mengstr/PlingPlong/Firmware/Controller/PlingPlong.X/easteregg.c

#include <stdint.h>         // uint8_t definitions
#include <string.h>         // strcpy for easteregg
#include <usart.h>

#include "config.h"
#include "dispbut.h"
#include "touch.h"
#include "easteregg.h"



const uint16_t hadLeds[]={
    0x7c9f,0x43f0,0x43f0,0x729f,    //  HTTP
    0x0140,0x6083,0x6083,0x7c9f,    //  ://H
    0x3e8f,0x462e,0x6c9f,0x3e8f,    //  ACKA
    0x3a3f,0x3e8f,0x60f8,0x0020,    //  DAY.
    0x462e,0x7e3f,0x7d9f            //  COM
};


//
// MIDI converted by Miditones https://code.google.com/p/miditones/ made by Len Shustek
//
const uint8_t eeMidiNyan [] = {
0x90,87, 0,102, 0x80, 0,3, 0x90,88, 0,102, 0x80, 0,3, 0x90,90, 0,102, 0x80, 0,109,
0x90,95, 0,102, 0x80, 0,3, 0x90,88, 0,102, 0x80, 0,3, 0x90,87, 0,102, 0x80, 0,3,
0x90,88, 0,102, 0x80, 0,3, 0x90,90, 0,102, 0x80, 0,3, 0x90,95, 0,102, 0x80, 0,3,
0x90,99, 0,102, 0x80, 0,3, 0x90,100, 0,102, 0x80, 0,3, 0x90,99, 0,102, 0x80, 0,3,
0x90,94, 0,102, 0x80, 0,3, 0x90,95, 0,102, 0x80, 0,109, 0x90,90, 0,102, 0x80, 0,109,
0x90,87, 0,102, 0x80, 0,3, 0x90,88, 0,102, 0x80, 0,3, 0x90,90, 0,102, 0x80, 0,109,
0x90,95, 0,102, 0x80, 0,109, 0x90,97, 0,102, 0x80, 0,3, 0x90,94, 0,102, 0x80, 0,3,
0x90,95, 0,102, 0x80, 0,3, 0x90,97, 0,102, 0x80, 0,3, 0x90,100, 0,102, 0x80, 0,3,
0x90,99, 0,102, 0x80, 0,3, 0x90,100, 0,102, 0x80, 0,3, 0x90,97, 0,102, 0x80, 0,3,
0x90,40, 0x91,78, 0,207, 0x81, 0,3, 0x80, 0x90,80, 0x91,52, 0,207, 0x80, 0,3, 0x81, 0x90,74,
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
0,117, 0x82, 0x80, 0,4, 0x90,37, 0x91,44, 0x92,49, 0,229, 0x80, 0x81, 0x82, 0,4, 0x90,35,
0x91,42, 0x92,47, 0,117, 0x93,68, 0,112, 0x83, 0,4, 0x93,68, 0,229, 0x80, 0x81, 0x82, 0x83,
0,4, 0x90,35, 0x91,68, 0x92,42, 0x93,80, 0,229, 0x81, 0x83, 0x80, 0x82, 0,4, 0x90,68, 0x91,35,
0x92,80, 0x93,42, 0,229, 0x80, 0x82, 0,4, 0x90,68, 0x92,80, 0,229, 0x81, 0x83, 0x80, 0x82, 0,4,
0x90,35, 0x91,68, 0x92,42, 0x93,80, 0,112, 0x81, 0x83, 0,4, 0x91,68, 0x93,80, 0,112, 0x80,
0x82, 0,4, 0x90,47, 0x92,54, 0,112, 0x83, 0x81, 0,117, 0x82, 0x80, 0,4, 0x90,35, 0x91,42,
0x92,47, 0,229, 0x80, 0x81, 0x82, 0,4, 0x90,68, 0x91,30, 0x92,80, 0x93,37, 0,229, 0x80, 0x82,
0,4, 0x90,68, 0x92,80, 0,229, 0x81, 0x83, 0x80, 0x82, 0,4, 0x90,30, 0x91,68, 0x92,37, 0x93,80,
0,229, 0x81, 0x83, 0x80, 0x82, 0,4, 0x90,68, 0x91,30, 0x92,80, 0x93,37, 0,229, 0x80, 0x82, 0,4,
0x90,68, 0x92,80, 0,229, 0x81, 0x83, 0x80, 0x82, 0,4, 0x90,30, 0x91,68, 0x92,37, 0x93,80, 0,112,
0x81, 0x83, 0,4, 0x91,68, 0x93,80, 0,112, 0x80, 0x82, 0,4, 0x90,42, 0x92,49, 0,112, 0x83,
0x81, 0,117, 0x82, 0x80, 0,4, 0x90,30, 0x91,37, 0x92,42, 0,229, 0x80, 0x81, 0x82, 0,4, 0x90,30,
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
};





void EeNoteOn(uint8_t no) {
    while (Busy2USART());
    Write2USART(0x90|CHANNEL);
    while (Busy2USART());
    Write2USART(no);
    while (Busy2USART());
    Write2USART(VELOCITY);
    __delay_ms(1);
}

void EeNoteOff(uint8_t no) {
    while (Busy2USART());
    Write2USART(0x80|CHANNEL);
    while (Busy2USART());
    Write2USART(no);
    while (Busy2USART());
    Write2USART(VELOCITY);
    __delay_ms(1);
}

void EeSendCC(uint8_t no, uint8_t v) {
    while (Busy2USART());
    Write2USART(0xB0|CHANNEL);
    while (Busy2USART());
    Write2USART(no);
    while (Busy2USART());
    Write2USART(v);
    __delay_ms(1);
}




void EeAllNotesOff(void) {
    uint8_t i;
    for (i=0; i<127; i++) {
        EeNoteOff(i);
    }
}


void EasterEgg(uint8_t mode) {
    uint8_t     i,j;
    uint8_t     tmps[20];
    uint16_t    noteCnt;
    uint8_t     eeChannelTone[16];
    uint8_t     b1,b2;
    uint16_t    ii, dly;
    uint8_t     *pMidi;


    // Step 1 - Silence all channels
    EeAllNotesOff();
    leds=0x00;
    disp[0]=0x00;
    disp[1]=0x00;
    disp[2]=0x00;

    // If mode is 1 display HTTP://HACKADAY.COM on 7-segs
    if (mode==1) {
        //           000111222333444555666777
        strcpy(tmps,"HTTP: // HACKADAY .  COM");
        for (i=0; i<8; i++) {
            disp[0]=charmap[tmps[0+((i)*3)]-32];
            disp[1]=charmap[tmps[1+((i)*3)]-32];
            disp[2]=charmap[tmps[2+((i)*3)]-32];
            for (j=0; j<40; j++) __delay_ms(10);
        }
    }

    // If mode is 2 display HTTP://HACKADAY.COM on the leds
    if (mode==2) {
        for (j=0; j<100; j++) __delay_ms(10);
        for (i=0; i<sizeof(hadLeds)/2; i++) {
            leds=hadLeds[i];
            for (j=0; j<40; j++) __delay_ms(10);
            leds=0;
            for (j=0; j<5; j++) __delay_ms(10);
        }
    }

    disp[0]=0x00;
    disp[1]=0x00;
    disp[2]=0x00;


    // Start playing tune
    if (mode==1) {
        EeSendCC(10,8); // Start with sound #8 plain sinus
        pMidi=eeMidiFox;// +821;
    } else {
        EeSendCC(10,16); // Start with sound #64
        pMidi=eeMidiNyan;
    }
    noteCnt=0;


    // Play the mididata
    for (;;) {
        b1=*pMidi;
        b2=*(pMidi+1);

        // End-Of-Song
        if ((b1&0xF0)==0xF0) {
            EeAllNotesOff();
            leds=0x00;
            disp[0]=0x00;
            disp[1]=0x00;
            disp[2]=0x00;
            return;
        }

        // Sound change
        if ((b1&0xF0)==0xA0) {
            EeSendCC(10,b2);
            pMidi+=2;
            continue;
        }


        // Note on
        if ((b1&0xF0)==0x90) {
            if (mode==2) b2=b2-12;  // Nyan is too high-pitched
            eeChannelTone[b1&0x0F]=b2;
            setbit(leds,b1&0xF);
            EeNoteOn(eeChannelTone[b1&0x0F]);
            pMidi+=2;
            noteCnt++;
            DispValue(noteCnt);
            continue;
        }

        // Note off
        if ((b1&0xF0)==0x80) {
            clrbit(leds,b1&0x0F);
            EeNoteOff(eeChannelTone[b1&0x0F]);
            pMidi+=1;
            continue;
        }

        // Delay
        if ((b1&0x80)==0x000) {
            dly=b1;
            dly=dly*256;
            dly=dly+b2;
            dly=dly/2;
            for (ii=0; ii<dly; ii++) __delay_ms(1);
            pMidi+=2;
            continue;
        }

    }
}
